SantaClawzzz/IronHand/Electronics/v1/Expo/Corner.jpg

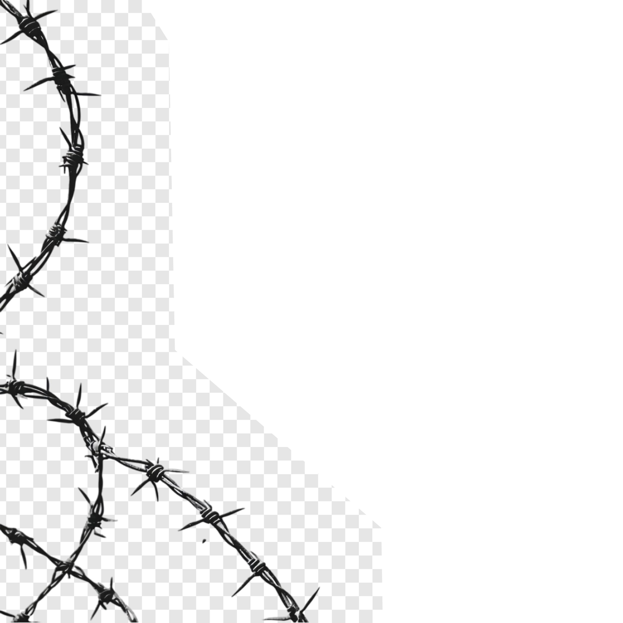
Electronics/v1/Expo/Corner.jpg
