SantaClawzzz/IronHand/Electronics/v1/Expo/tagilla.png

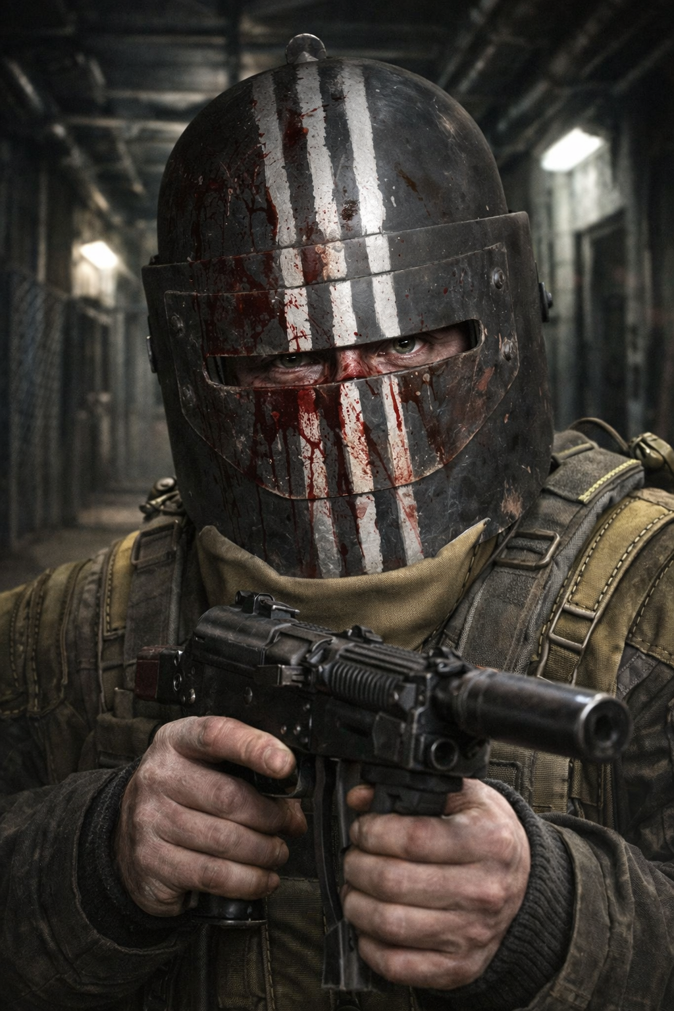
Electronics/v1/Expo/tagilla.png
